mafe72/27c160-tl866-adapter/kicad-project/back.png

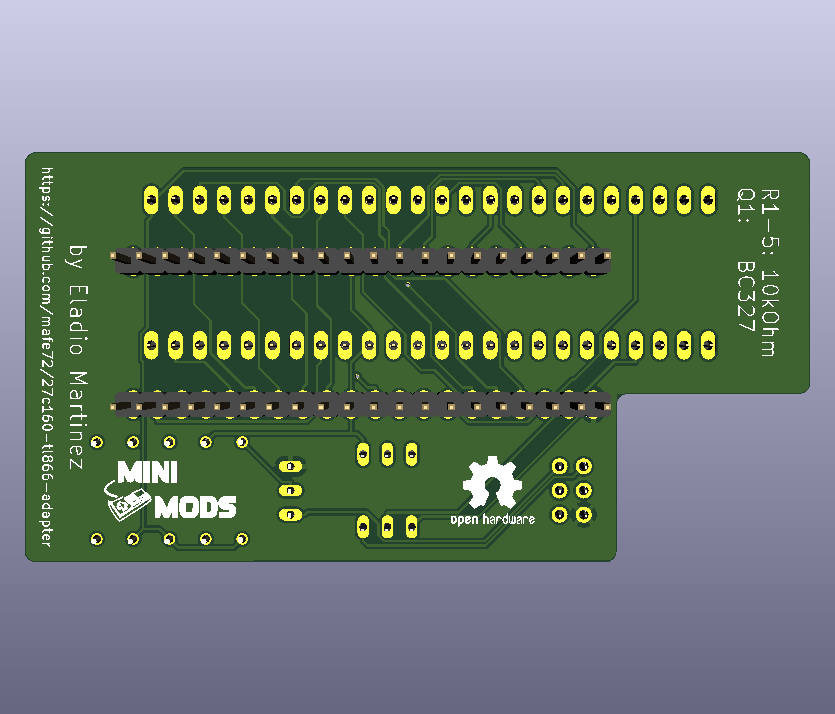
kicad-project/back.png
